patchinc/heartypatch/docs/images/app-shot2.png

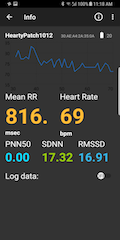
docs/images/app-shot2.png
