patchinc/heartypatch/docs/images/heartypatch-small.jpg

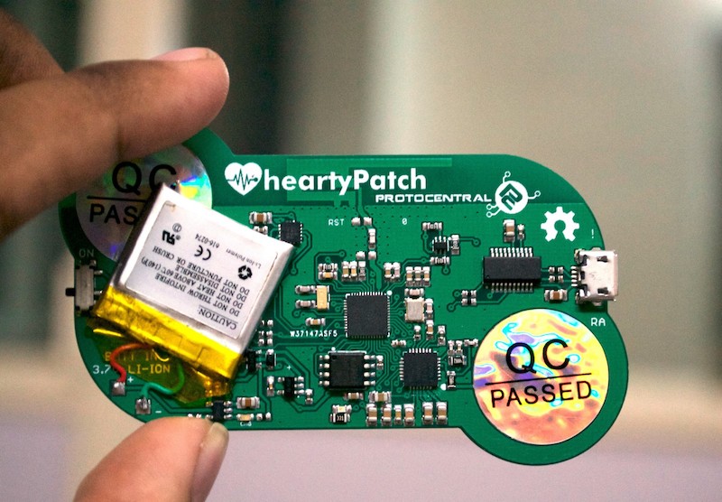
docs/images/heartypatch-small.jpg
