patchinc/heartypatch/firmware/heartypatch-ble/main/heartypatch_arrhythmia.c

#include <stdio.h>
#include <stdlib.h>
#include <math.h>
#include <string.h>
#include "freertos/FreeRTOS.h"
#include "esp_wifi.h"
#include "esp_system.h"
#include "esp_event.h"
#include "esp_event_loop.h"
#include "nvs_flash.h"
#include "driver/gpio.h"
#include "driver/spi_master.h"
#include "bt.h"
#include "driver/ledc.h"
#include "driver/uart.h"

#include "heartypatch_max30003.h"
#include "heartypatch_ble.h"
#include "heartypatch_arrhythmia.h"

uint8_t arrhythmiadetector = 0x00;

float rr_new[MAX-1][2]={0};
float sum[MAX-1]={0};
float os[MAX-1]={0};
float drr[MAX-1][2]={0};
float drr_s[MAX-1]={0};
float drrnew[MAX-1][2]={0};
unsigned int z[30][30]={0};
unsigned int z2[30][30]={0};
unsigned int z3[30][30]={0};
unsigned int flipz3[30][30]={0};
unsigned int flipz4[30][30]={0};
unsigned int z4[30][30]={0};
unsigned int z1[30][30]={0};

int origincount=0;
int i,j,h,y=0;

int		BC1		= 		0;
int		BC2		= 		0;
int		BC3		= 		0;
int		BC4		= 		0;
int		BC5		= 		0;
int		BC6		= 		0;
int		BC7		= 		0;
int		BC8		= 		0;
int		BC9		= 		0;
int		BC10	= 		0;
int		BC11	= 		0;
int		BC12	= 		0;
int		PC1		= 		0;
int		PC2		= 		0;
int		PC3		= 		0;
int		PC4		= 		0;
int		PC5		= 		0;
int		PC6		= 		0;
int		PC7		= 		0;
int		PC8		= 		0;
//int		PC9		= 		0;
int		PC10	= 		0;
//int		PC11	= 		0;
int		PC12	= 		0;

int a=0;
float start = -0.58;
int IrrEv;
int PACEv;
float AFEv;
int BC=0;
int PC=0;
int bdc=0;
int pdc=0;
int n=14;
int tally =0;
float verify=0;
//float comput_AFEv(float array_temp[]); //conflicting types error

void challenge(float array_temp[])
{
	AFEv=0.00;
	AFEv = comput_AFEv(array_temp);
//	printf("%f\n",AFEv);
	if(AFEv>1)
	{
		arrhythmiadetector= 0xff;
	}
	else
	{
		arrhythmiadetector = 0x1f;
	}
	
}
float comput_AFEv(float array_temp[])
{
	drrf(array_temp);
	metrics(drr_s);
	AFEv=IrrEv-origincount-2*PACEv;
	return AFEv;
}
void drrf(float array_temp[])
{
	for(i=0;i<(MAX-1);i++)
	{
		rr_new[i][0] = array_temp[i+1];
		rr_new[i][1] = array_temp[i];
        if((rr_new[i][0]<0.5)||(rr_new[i][1]<0.5))
		{
			drr_s[i] = 2*(rr_new[i][0]-rr_new[i][1]);
		}
		else if((rr_new[i][0]>1)||(rr_new[i][1]>1))
		{
			drr_s[i] = 0.5*(rr_new[i][0]-rr_new[i][1]);

		}
		else
		{	
			drr_s[i]= (rr_new[i][0]-rr_new[i][1]);
	    }
	}

}
void metrics( float drr_s[])
{
	origincount = 0;
	tally=0;
	IrrEv=0;
	PACEv=0;

	int		BC1		= 		0;
	int		BC2		= 		0;
	int		BC3		= 		0;
	int		BC4		= 		0;
	int		BC5		= 		0;
	int		BC6		= 		0;
	int		BC7		= 		0;
	int		BC8		= 		0;
	int		BC9		= 		0;
	int		BC10	= 		0;
	int		BC11	= 		0;
	int		BC12	= 		0;
	int		PC1		= 		0;
	int		PC2		= 		0;
	int		PC3		= 		0;
	int		PC4		= 		0;
	int		PC5		= 		0;
	int		PC6		= 		0;
	int		PC7		= 		0;
	int		PC8		= 		0;
//	int		PC9		= 		0;
	int		PC10	= 		0;
//	int		PC11	= 		0;
	int		PC12	= 		0;

	for(i=0;i<(MAX-2);i++)
	{
		drr[i][0] = drr_s[i+1];
		drr[i][1] = drr_s[i];
		if(((fabs(drr[i][0]))<=0.02)&&((fabs(drr[i][1]))<=0.02))
	    {
			origincount++;
        }
	}

  	for(i=0;i<(MAX-2);i++)
	{
		if((fabs(drr[i][0])<=1.5)&&(fabs(drr[i][1])<=1.5))
	    {
		drrnew[tally][0]=drr[i][0];
	    drrnew[tally][1]=drr[i][1];
		tally++;
	    }
	}
	for(i=0;i<30;i++)
	{
		for(j=0;j<30;j++)
		{
			z[i][j]=0;
		}
	}


	for(j=0;j<30;j++)
	{
		for(h=0;h<30;h++)
		{
			for(i=0;i<tally;i++)
			{
				if(((drrnew[i][0])>(-0.60+0.04*(float) j))&&((drrnew[i][0])<=(-0.60+0.04*(((float) j)+1)))&&((drrnew[i][1])>(-0.60+0.04*(float) h))&&((drrnew[i][1])<=(-0.60+0.04*(((float) h)+1))))
				{
					z[j][h]++;
				}
			}
		}
	}

	for(h=0;h<30;h++)
	{
		for(i=0;i<tally;i++)
		{
			if((drrnew[i][0]<=(-0.60))&&(drrnew[i][1]<=(-0.60)))
			{
					z[0][0]++;

			}

			else if((drrnew[i][0]<=(-0.60))&&((drrnew[i][1])>(-0.60+0.04*h))&&((drrnew[i][1])<=(-0.60+0.04*(h+1))))
			{
					z[0][h]++;

			}
		}
	}


	for(h=0;h<30;h++)
	{
		for(i=0;i<tally;i++)
		{
		    if((drrnew[i][0]>(0.60))&&(drrnew[i][1]>(0.60)))

				{
					z[29][29]++;

				}

			else if((drrnew[i][0]>(0.60))&&((drrnew[i][1])>(-0.60+0.04*h))&&((drrnew[i][1])<=(-0.60+0.04*(h+1))))
				{

					z[29][h]++;


				}
		}

	}


	for(h=0;h<30;h++)
	{
		for(i=0;i<tally;i++)
		{
		   if((drrnew[i][1]>(0.60))&&((drrnew[i][0])>(-0.60+0.04*h))&&((drrnew[i][0])<=(-0.60+0.04*(h+1))))
			{
				z[h][29]++;

			}
		}
	}

	for(h=0;h<30;h++)
	{
			for(i=0;i<tally;i++)
			{
			   if((drrnew[i][1]<=(-0.60))&&((drrnew[i][0])>(-0.60+0.04*h))&&((drrnew[i][0])<=(-0.60+0.04*(h+1))))
				{

					z[h][0]++;


				}
			}

	}
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
				{
					bdc++;
					pdc=pdc+diag[i];
				}
				j++;

		}
	}

	BC = BC+bdc;
	PC = PC+pdc;
	bdc=0;
	pdc=0;
	i=0;

 	 // otaining main diagonal elements
	for(j=0;j<=n;j++)
	{
		diag[j]=z2[i][j];
		z2[i][j]=z2[i][j]-diag[j];
		  if (diag[j] != 0)
		{
			bdc++;
			pdc=pdc+diag[j];
		}
		i++;
	}

	BC = BC+bdc;
	PC = PC+pdc;

}
